agsb/jelly/jellys/extras/1bit-d-flip-flop.png

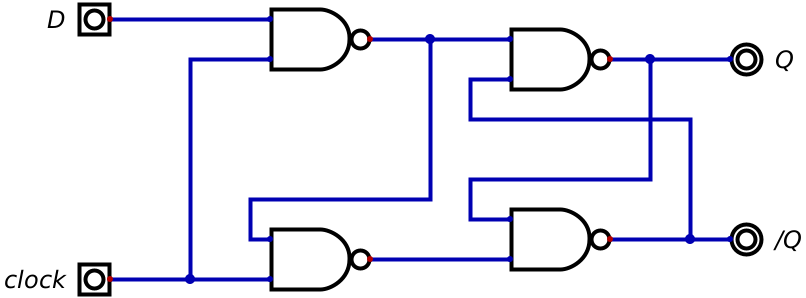
jellys/extras/1bit-d-flip-flop.png
